mrlcosta/Contador-de-vagas-UFABC/firmware/src/test.c

/***************************************************************
 * Biblioteca de Teste da PCI PRO4.38                          *
 ***************************************************************/
 
 /* Autor: Felipe Antonio Montagneri Lucchini
    Data : 02/01/2017
	*/
	
/***************************************************************/

#include "stm8s.h"
#include "stm8s_io.h"
#include "stm8s_timer.h"

#include "test.h"

#define FINISH 81
#define DELAY  82

uint8_t   state       = 0;
uint8_t   stack       = 0;
uint8_t   delay       = 0;
uint8_t   model_out   = 1;
uint8_t   model_in    = 0;
uint8_t   menuState   = 0;
uint8_t   selectState = 0;

uint16_t *buffer      = (uint16_t *)0;

bool      debouncing1 =  FALSE;
bool      debouncing2 =  FALSE;
bool      ack         =  FALSE;
bool      buzzer      =  FALSE;
bool      blink       =  FALSE;
bool      menu        =  TRUE;
bool      start       =  TRUE;
bool      wait        =  TRUE;





/***************************************************************
 * Funções e Procedimentos                                     *
 ***************************************************************/
/***************************************************************
 * testUpdate();                                               *
 *                                                             *
 * Procedimento de Controle de Teste;                          *
 *                                                             *
 * uint8_t *control -> endereço da variável de controle;       *
 *                                                             *
 * void -> não retorna valor;                                  *
 ***************************************************************/
void testUpdate(uint8_t *control){
	 
	 if(*control >= 31){
		 
		 return;
		 
	  }
	 
	 if(((*buffer > 500)&&(*buffer < 4500))||(*(buffer + 2) < 500)){
		 
		 *control  = 0;
		  state    = 0;
			ack      = FALSE;
			wait     = TRUE;
			
		 timerEnable(2, DISABLE);
		 timerReset (2);
		 
		 timerReset (6);
			
		 ioCommSetDir(INPUT);
		 
		 return;
		 
	  }else{
			
		 if((state == 0)&&(*control < 3)){
			 
			 if(*control == 0){
			   
			   timerSetOverflowValue(6, 500);
			   timerReset           (6);
			   timerEnable          (6, ENABLE);
			   
			  }
				
			 *control = 1;
				
		  }
			
		}
		
	 if(*buffer > 4500){
		 
		 *control = 4;
		 
		 return;
		 
	  }
		
	 if(!timerGetOverflow(6) && wait){
		 
		 ack = FALSE;
		 
		 return;
		 
	  }else{
			
		 wait = FALSE;
		 
		 timerEnable(6, DISABLE);
		 timerReset (6);
			
	  }	 
		
	 if((state == 0)&&(*control >= 3)&&(*control < 31)){
		 
		 if(buzzer){
			 
			 buzzer = FALSE;
			 menu   = TRUE;
			 
			 if(*control == 3){
				 
				 timerSetOverflowValue(3, 1000);
				 timerReset           (3);
				 timerEnable          (3, ENABLE);
				 
				 blink = TRUE;
				 
			  }else{
					
				 timerSetOverflowValue(1, 500);
				 timerReset           (1);
				 timerEnable          (1, ENABLE);	
					
				}
			 
		  }
			
		 if(timerGetOverflow(1)){
			 
			 timerReset(1);
			 
			 if(blink){
				 
				 blink = FALSE;
				 
			  }else{
					
				 blink = TRUE;	
					
				}
			 
		  }
			
		 if(!timerGetOverflow(3) && blink){
					
			 if(timeBase210us()){
			   
				// GPIO_WriteReverse(BUZZER);
				 
			  }
				
			}else{
				
			 GPIO_WriteLow(BUZZER);	
				
			}
			
		}
		
	 if(timerGetOverflow(2)){
		 
		 if(!GPIO_ReadInputPin(COMM)&&(*control != 0)){
			 
			 ack = TRUE;
			 
		  }
			
		 timerEnable(2, DISABLE);	
		 timerReset (2);	 
		 
	  }
	 
   switch(state){
		 
		 case 0:	 
			 
			 GPIO_WriteLow(CH1);
			 GPIO_WriteLow(CH2);
			 GPIO_WriteLow(CH3);
			 GPIO_WriteLow(CH4);
			 GPIO_WriteLow(IGN);
			 GPIO_WriteLow(DOOR);
			 GPIO_WriteLow(SETA);
			 GPIO_WriteLow(SW_P);
			 GPIO_WriteLow(SW_N);
			 GPIO_WriteLow(I_MOT);
			 GPIO_WriteLow(CMD_DN);
			 GPIO_WriteLow(CMD_UP); 
			 
			 if(ack){				 
				 
				 
				 *control = 2;
				  ack     = FALSE;
					menu    = FALSE;
				  buzzer  = TRUE;
				  state   = 1;			 
					
			   timerSetOverflowValue(3, 30);			     
			   timerReset           (3);			     			 
				 timerEnable          (3, ENABLE);	
				  
				 ioCommSetDir(OUTPUT);
					
			  }
			 
		 break;
/***************************************************************/		 
     case 1:      
			 
			 if(timerGetOverflow(3)){
				 
				 model_in++;
				 
				 if(model_in <= (2 * model_out)){
					  
					 GPIO_WriteReverse(COMM);
					 
					 timerSetOverflowValue(1, 1500);
				   timerReset           (1);
				   timerEnable          (1, ENABLE);
				   
				   timerReset           (3);
				    
				  }else{
						
					 model_in = 0;					 
					 state    = 2;
					 
					 timerEnable(1, ENABLE);
					 timerReset (1);
					 
					 ioCommSetDir(INPUT);
						
					}
				  
			  }
			 
			 
			 
			 
		 break;
/***************************************************************/	
     case 2:
		   
			 if(ack){
				 
				 ack = FALSE;
				 
				 if(model_in == 0){
					 
					 timerSetOverflowValue(1, 50);
					 timerReset           (1);
					 timerEnable          (1, ENABLE);
					 
				  }else{
						
					 timerReset(1);
						
					}
				 
				 model_in++;
				 
			  }			  
				
			 if(timerGetOverflow(1)){
				 
				 if(model_in == model_out){
					 
					  buzzer  = TRUE;
					  state   = DELAY;
					  stack   = 3;
				    
				   timerReset (1);
					  
					 timerSetOverflowValue(3, 15);	
				   timerReset           (3);			     			 
				   timerEnable          (3, ENABLE);
           
				   ioCommSetDir(OUTPUT);
					 
				   GPIO_WriteHigh(COMM);					 
					 
				  }else{
				   
					 *control = 5;
				    state   = FINISH;
					 
				  }
					
				 model_in = 0;
				 
			  }
       
		 break;		 
/***************************************************************/	
		 case 3:
		    
			 if(ack){
				 
				 ack   = FALSE;
				 state = DELAY;
				 stack = 4;
				 
				 timerReset (1);
				 
				 timerReset (3);
				 timerEnable(3, ENABLE);
				  
				 ioCommSetDir(OUTPUT);
				  
				 GPIO_WriteHigh(COMM);			 
				 
		    }		
				
			 if(timerGetOverflow(1)){
				 
				 *control =  7;
				  state   = FINISH;
				  
			  }				
			 
		 break;
/***************************************************************/			 
		 case 4:
		    
			 if(ack){
				 
				 ack   = FALSE;
				 state = DELAY;
				 stack = 5;
					
				 timerReset (1);
				 
				 timerReset (3);
				 timerEnable(3, ENABLE);	
				 
				 ioCommSetDir(OUTPUT);
				  
				 GPIO_WriteHigh(COMM);
				 
		    }		
				
			 if(timerGetOverflow(1)){
				 
				 *control =  7;
				  state   = FINISH;
				  
			  }				
			 
		 break;
/***************************************************************/			 
		 case 5:
		    
			 if(ack){
				 
				 ack   = FALSE;;
				 state = DELAY;
				 stack = 6;
					
				 timerReset (1);
				 
				 timerReset (3);
				 timerEnable(3, ENABLE);	
				 
				 GPIO_WriteHigh(SETA);
				 
				 ioCommSetDir(OUTPUT);
				  
				 GPIO_WriteHigh(COMM);
				 
		    }		
				
			 if(timerGetOverflow(1)){
				 
				 *control =  8;
				  state   = FINISH;
				 
			  }				
			 
		 break;
/***************************************************************/			 
		 case 6:
		    
			 if(ack){
				 
				 ack   = FALSE;
				 state = DELAY;
				 stack = 7;
					
				 timerReset (1);
				 
				 timerReset (3);
				 timerEnable(3, ENABLE);	
				 
				 GPIO_WriteLow(SETA);
				 
				 ioCommSetDir(OUTPUT);
				  
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
		  }
		 
		 if(ack){
				 
				  ack     = FALSE;					
				 *control = 3;
				  state   = FINISH;
					
				 timerEnable(1, DISABLE);
				 timerReset (1);
				 
				 timerEnable(3, DISABLE);
				 timerReset (3);
          
		    }		
				
			 if(timerGetOverflow(1)){
				  
				 *control = 30;
				  state   = FINISH;	 
			   
			  }			       
		 
		 
		 break;
/***************************************************************/
     case FINISH:
		   
		   if(timerDelay(500)){
				 
				 GPIO_WriteLow(CH1);
		     GPIO_WriteLow(CH2);
		     GPIO_WriteLow(CH3);
		     GPIO_WriteLow(CH4);
			   GPIO_WriteLow(IGN);
			   GPIO_WriteLow(DOOR);
			   GPIO_WriteLow(SETA);
			   GPIO_WriteLow(SW_P);
			   GPIO_WriteLow(SW_N);
			   GPIO_WriteLow(I_MOT);
		     GPIO_WriteLow(CMD_DN);
		     GPIO_WriteLow(CMD_UP); 
				 
				 ack    = 0;
				 state  = 0;			 
				 buzzer = TRUE;
				 
				 if(*control != 3){
				   
				   menu  = TRUE;
					 
				  }
				 
				 timerEnable(2, DISABLE);
				 timerReset (2);
				 
			  }
		   
		 break;
/***************************************************************/		
		 case DELAY:
		    
		   if(timerGetOverflow(3)){
				 
				 GPIO_WriteLow (COMM);
				 
				 ioCommSetDir(INPUT);
				 
				 timerEnable(2, DISABLE);
				 timerReset (2);
				 
				 timerEnable(3, DISABLE);
				 timerReset (3);
				 
				 state = stack;
				 
			  } 
			  
		 break;
/***************************************************************/		 
	  }
	 
  }
	
/***************************************************************
 * menuUpdate(&control, &model);                               *
 *                                                             *
 * Procedimento de seleção do modelo da PCI;                   *
 *                                                             *
 * uint8_t *control -> endereço da variável de controle;       *
 * uint8_t *model   -> modelo selecionado;                     *
 *                                                             *
 * void -> não retorna valor;                                  *
 ***************************************************************/	
void menuUpdate(uint8_t *control, uint8_t *model){
	 
	 *model = model_out;
	 
	 if(!menu){
		 
		 return;
		 
	  }
		
	 switch(menuState){
		 
		 case 0:
		   
		   if(*(buffer + 3) > 500){
		     
		     timerEnable(4, DISABLE);
		     timerReset (4);
          
		     debouncing1 = FALSE;
		     
	      }else{
			   
		     if(!debouncing1){
			     
			     timerSetOverflowValue(4, 100);
					 timerReset           (4);
			     timerEnable          (4, ENABLE);
			     
			     debouncing1 = TRUE;		 
			     
		      }
			    
			   if(timerGetOverflow(4)){
			     
			     debouncing1 = FALSE;
					 
					 timerEnable(4, DISABLE);
		       timerReset (4);
			     
			     menuState++;
				   
			    }		
			   
		    }   
		   
		 break;
		 
		 case 1:
		   
			 if(*(buffer + 3) > 500){
				 
				 if((*control < 31)||(*control == 65)){
					  
					 *control = 31;
					 
				  }else{
						
					 *control += 1;
						
					}		
           
         menuState = 0;
				 
			  }
			 
		 break;
		 
		 
	  }
		
		switch(selectState){
		 
		 case 0:
		   
		   if(*(buffer + 4) > 500){
		     
		     timerEnable(5, DISABLE);
		     timerReset (5);
          
		     debouncing2 = FALSE;
		     
	      }else{
			   
		     if(!debouncing2){
			     
			     timerSetOverflowValue(5, 100);
					 timerReset           (5);
			     timerEnable          (5, ENABLE);
			     
			     debouncing2 = TRUE;		 
			     
		      }
			    
			   if(timerGetOverflow(5)){
			     
			     debouncing2 = FALSE;
					 
					 timerEnable(5, DISABLE);
		       timerReset (5);
			     
			     selectState++;
				   
			    }		
			   
		    }   
		   
		 break;
		 
		 case 1:
		   
			 if(*(buffer + 4) > 500){
				 
				 model_out = *control - 30;
				 
				 *control  = 0;
				 
         selectState = 0;
				 
			  }
			 
		 break;
		 
		 
	  }
		
	  
	 
	}
	
/***************************************************************
 * testStop(&control);                                         *
 *                                                             *
 * Procedimento de parada do teste;                            *
 *                                                             *
 * uint8_t *control -> endereço da variável de controle;       *
 *                                                             *
 * void -> não retorna valor;                                  *
 ***************************************************************/	
void testStop (uint8_t *control){
	 
	 *control = 6;
	    state = 0;
	 
	}
 
/***************************************************************
 * testSetBuffer(&bufferAddr);                                 *
 *                                                             *
 * Procedimento de seleção do endereço do buffer dos AD's;     *
 *                                                             *
 * uint16_t *bufferaddr -> endereço do buffer;                 *
 *                                                             *
 * void -> não retorna valor;                                  *
 ***************************************************************/
void testSetBuffer(uint16_t *bufferAddr){
	 
	 buffer = bufferAddr; 
	 
  }
	
/***************************************************************
 * Interrupção dos Ports;                                     *
***************************************************************/ 
INTERRUPT_HANDLER(EXTI_PORTA_IRQHandler, 3){
		
	 timerSetOverflowValue(2, 10);
	 timerReset           (2);
	 timerEnable          (2, ENABLE);
	 
	 if(state >= 48){
		 
		 GPIO_WriteReverse(SW_P);
		 
	  }
	  
  }
	
INTERRUPT_HANDLER(EXTI_PORTB_IRQHandler, 4){
	 
  }
	
INTERRUPT_HANDLER(EXTI_PORTC_IRQHandler, 5){
		
	}
	
INTERRUPT_HANDLER(EXTI_PORTD_IRQHandler, 6){
    
  }
	
INTERRUPT_HANDLER(EXTI_PORTE_IRQHandler, 7){
	 	 
  }
 
